anton2026gamca/lnx-infrabot/hardware/3d_models/stl/omniwheel_base.stl

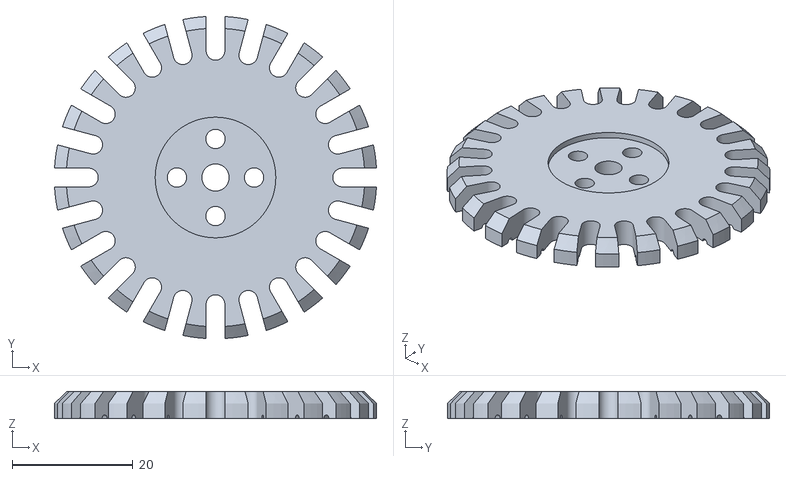
[picture p16: CAD file, 2026-06-06]
hardware/3d_models/stl/omniwheel_base.stl
53.4 x 53.4 x 4.50
