anton2026gamca/lnx-infrabot/hardware/3d_models/stl/uppest_part.stl

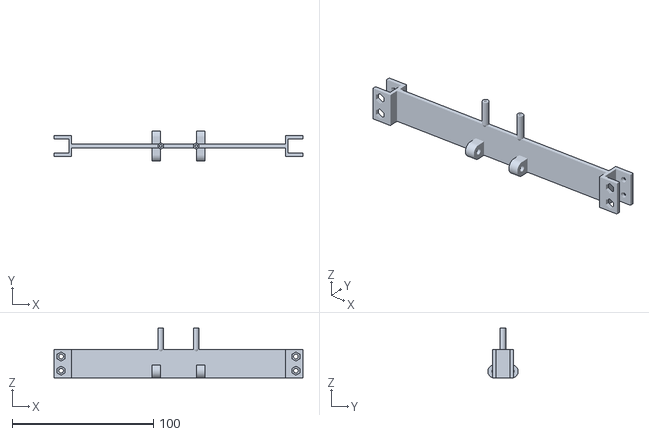
[picture p17: CAD file, 2026-06-06]
hardware/3d_models/stl/uppest_part.stl
176.0 x 21.5 x 35.0
