anton2026gamca/lnx-infrabot/hardware/3d_models/stl/middle_part.stl

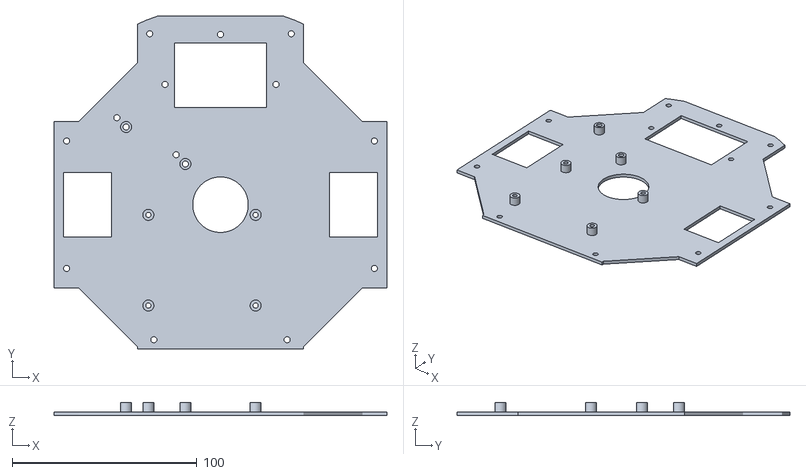
[picture p18: CAD file, 2026-06-06]
hardware/3d_models/stl/middle_part.stl
180.0 x 180.0 x 7.00
