anton2026gamca/lnx-infrabot/hardware/3d_models/stl/line_sensor_shield.stl

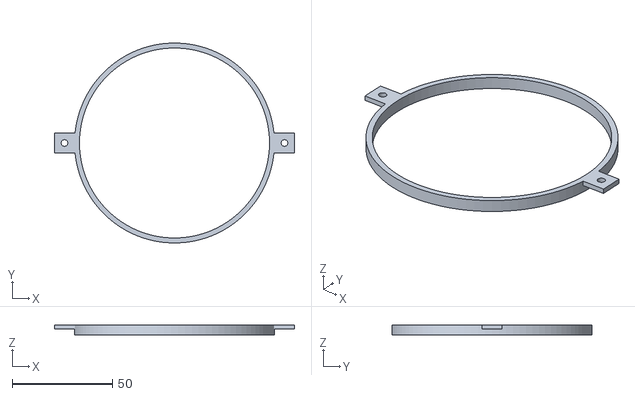
[picture p19: CAD file, 2026-06-06]
hardware/3d_models/stl/line_sensor_shield.stl
120.0 x 99.9 x 5.00
