anton2026gamca/lnx-infrabot/hardware/3d_models/stl/handle.stl

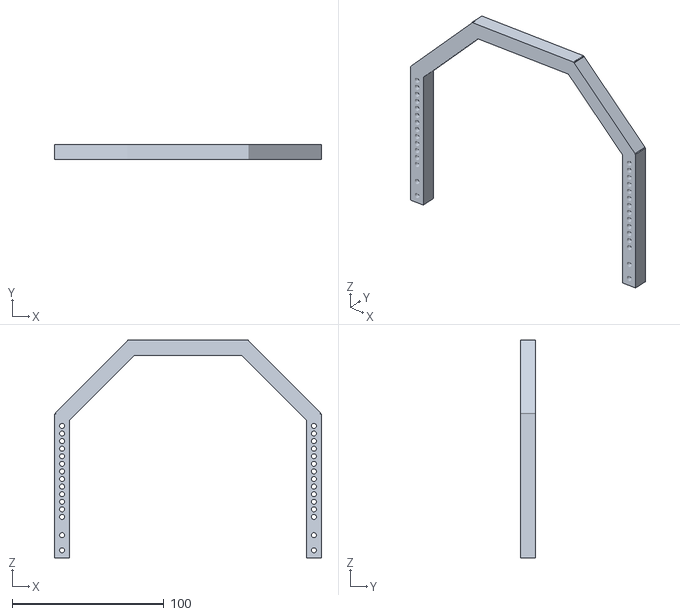
[picture p20: CAD file, 2026-06-06]
hardware/3d_models/stl/handle.stl
176.0 x 10.0 x 143.6
