anton2026gamca/lnx-infrabot/hardware/3d_models/stl/handle_bracket.stl

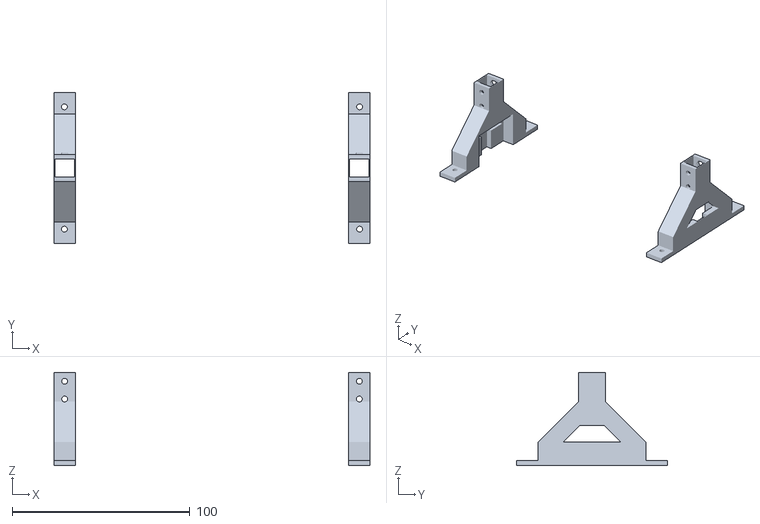
[picture p21: CAD file, 2026-06-06]
hardware/3d_models/stl/handle_bracket.stl
178.0 x 85.0 x 52.5
