anton2026gamca/lnx-infrabot/hardware/3d_models/stl/bottom_part.stl

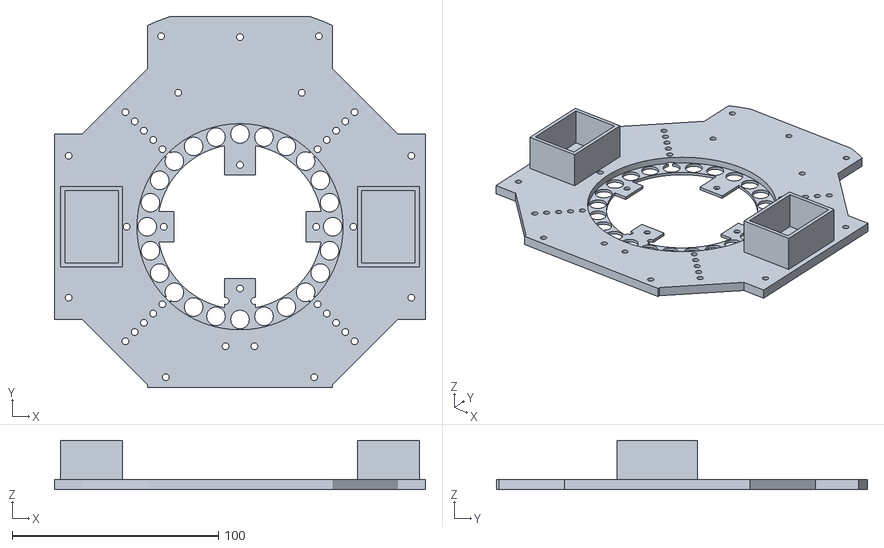
[picture p22: CAD file, 2026-06-06]
hardware/3d_models/stl/bottom_part.stl
180.0 x 180.0 x 24.0
