anton2026gamca/lnx-infrabot/hardware/3d_models/stl/top_markers.stl

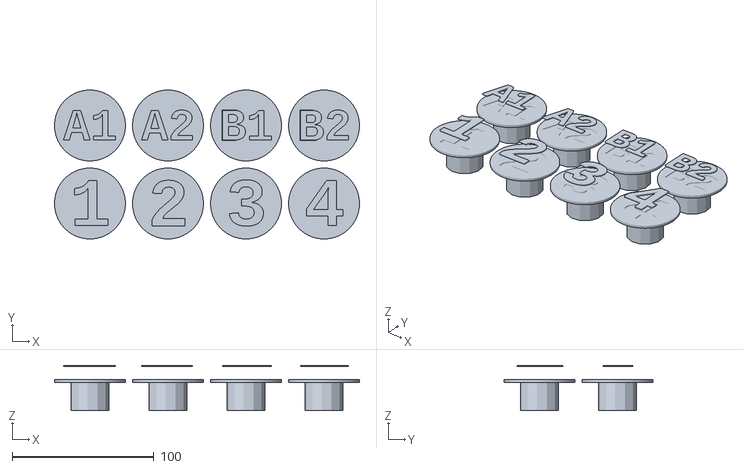
[picture p23: CAD file, 2026-06-06]
hardware/3d_models/stl/top_markers.stl
215.0 x 105.0 x 32.0
