anton2026gamca/lnx-infrabot/hardware/3d_models/stl/motor_driver_bracket.stl

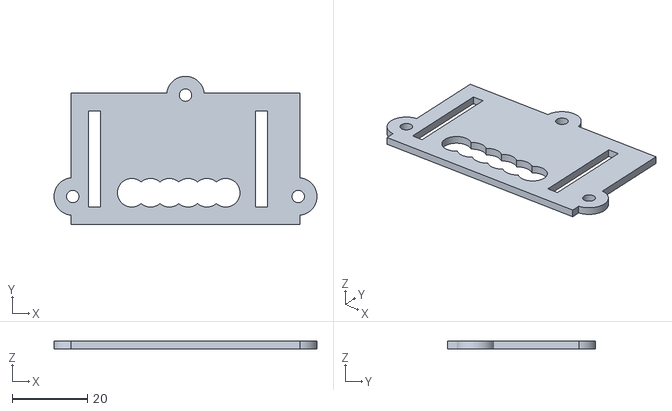
[picture p24: CAD file, 2026-05-19]
hardware/3d_models/stl/motor_driver_bracket.stl
70.0 x 39.5 x 2.00
